TheSuperiorMostafa/Shaper-Drone/3D files/Drone/SolidWorks Files/FRAME RE DO 4-19-26 IN PROG.SLDPRT

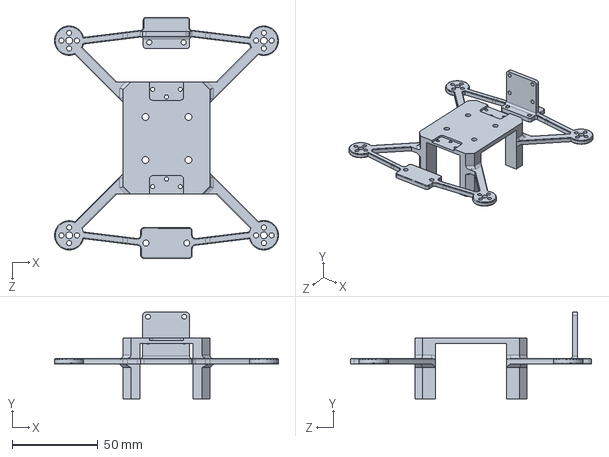
[picture p16: CAD file, 2026-04-30]
3D files/Drone/SolidWorks Files/FRAME RE DO 4-19-26 IN PROG.SLDPRT
130.3 x 50.5 x 140.2 mm
