TheSuperiorMostafa/Shaper-Drone/3D files/Drone/.STL Files/frame only 3-30-26.STL

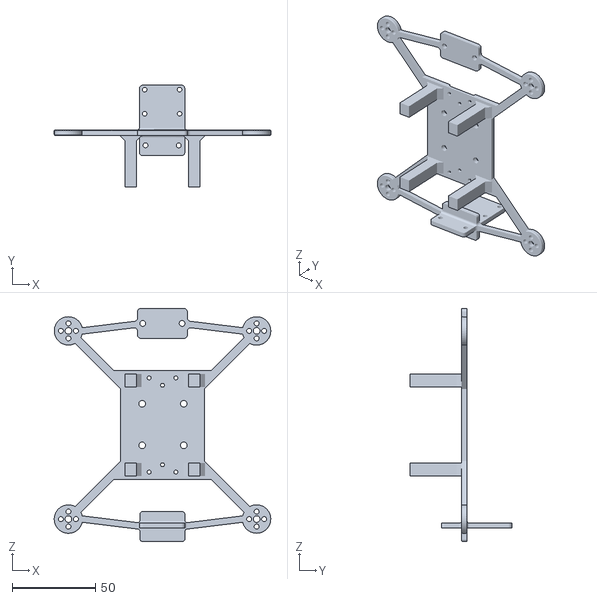
[picture p17: CAD file, 2026-04-30]
3D files/Drone/.STL Files/frame only 3-30-26.STL
130.3 x 61.2 x 140.2
