TheSuperiorMostafa/Shaper-Drone/3D files/Drone/.STL Files/DRONE FRAME  WITH PI MOUNT - MODULAR 1-21-26.STL

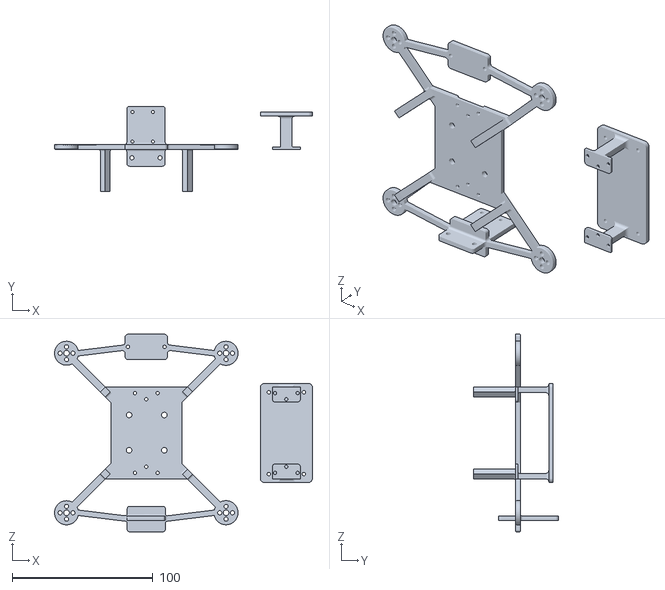
[picture p18: CAD file, 2026-04-30]
3D files/Drone/.STL Files/DRONE FRAME WITH PI MOUNT - MODULAR 1-21-26.STL
183.1 x 60.5 x 140.2
